tjb36/Environment-Monitor/Environment_Monitor_LTSPICE/AnalogInputScaling.asc

U1: LT1997-2
V1: voltage; SINE(0 10 3 0)
V_ref: voltage; 2.048V
Named nets: +5V, 0, V_out, V_in+, V_in-
V98 +5V 0 5 
.tran 1
Gain = x 0.2
MAX6126AASA21+
Voltage reference
